prajna-pranab/SFT/STL/asm_SFT-Mk4-SFTRocker.stl

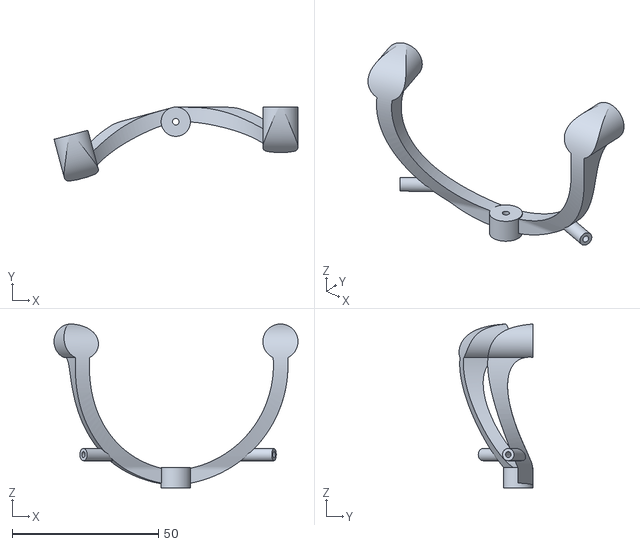
[picture p15: CAD file, 2024-05-06]
STL/asm_SFT-Mk4-SFTRocker.stl
83.3 x 25.2 x 56.0
