prajna-pranab/SFT/STL/asm_SFT-Mk4-SFTFlywheel Axle.stl

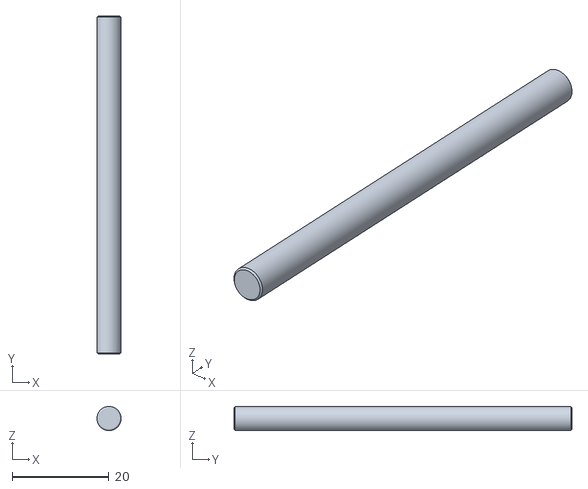
[picture p16: CAD file, 2024-05-06]
STL/asm_SFT-Mk4-SFTFlywheel Axle.stl
5.00 x 70.0 x 5.00
