prajna-pranab/SFT/STL/asm_SFT-Mk4-SFTSlider Block.stl

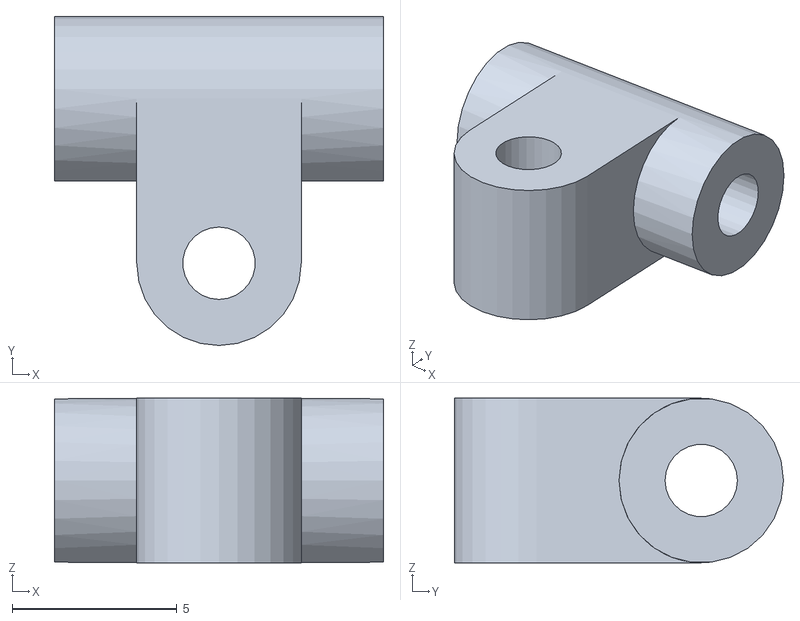
[picture p17: CAD file, 2024-05-06]
STL/asm_SFT-Mk4-SFTSlider Block.stl
10.0 x 10.0 x 5.00
