prajna-pranab/SFT/STL/asm_SFT-Mk4-SFTPin Bar.stl

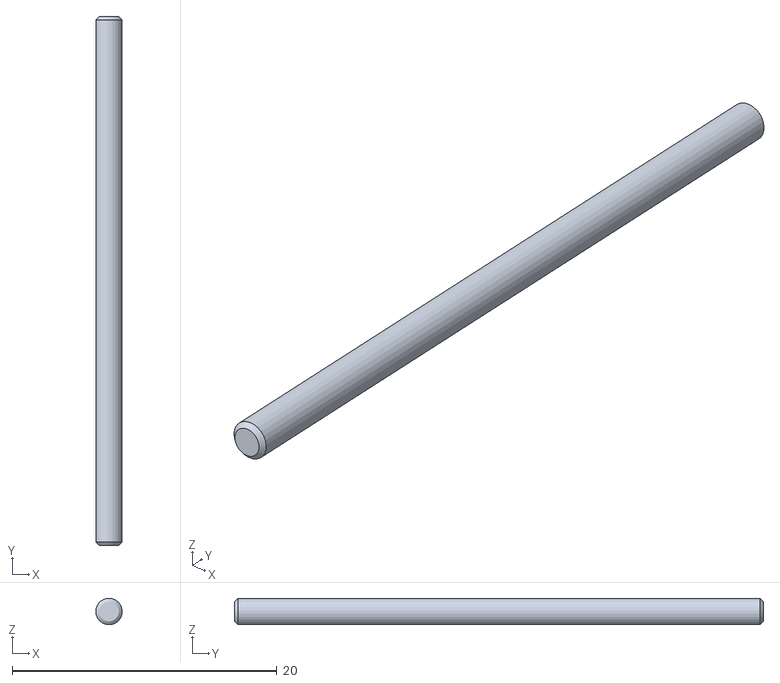
[picture p18: CAD file, 2024-05-06]
STL/asm_SFT-Mk4-SFTPin Bar.stl
2.00 x 40.0 x 2.00
