prajna-pranab/SFT/STL/asm_SFT-Mk4-SFTFlywheel Weight.stl

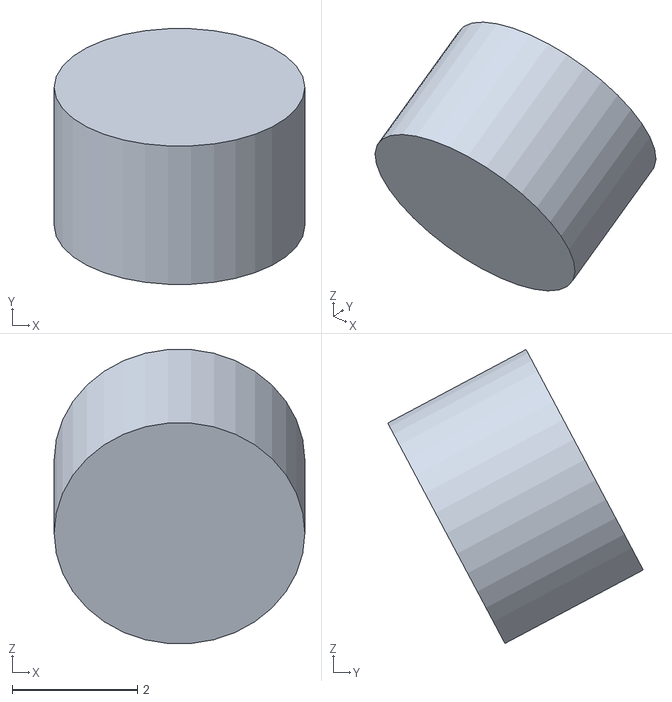
[picture p19: CAD file, 2024-05-06]
STL/asm_SFT-Mk4-SFTFlywheel Weight.stl
4.00 x 4.08 x 4.69
