prajna-pranab/SFT/asm_SFT-Mk4.FCStd

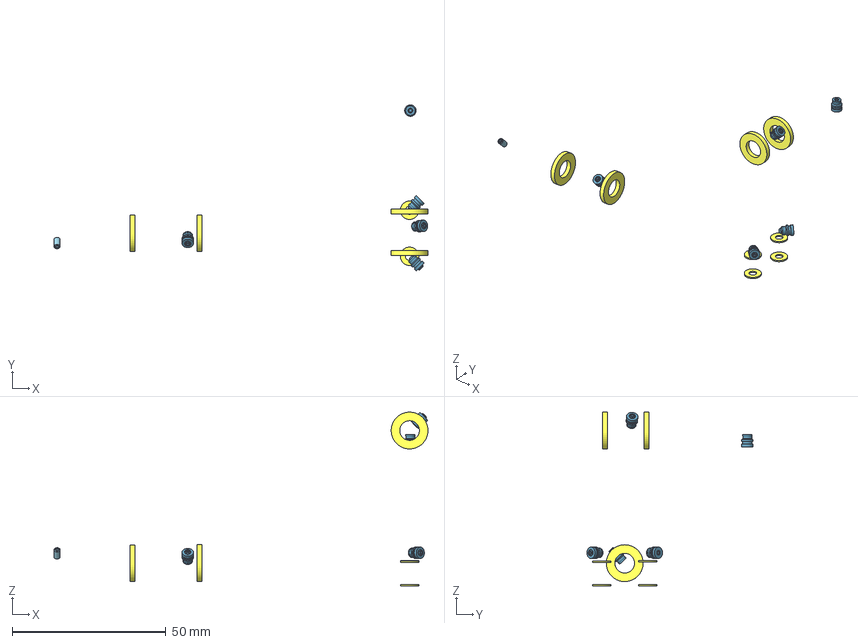
[picture p20: CAD file, 2024-04-28]
asm_SFT-Mk4.FCStd
121.8 x 54.1 x 56.6 mm
M6-Washer x 3
M2x4-Insert x 3
M2x4-Screw x 3
M6-Washer1773 x 3
M2x4-Insert19512 x 3
M2x5-Screw x 3
M2.5-Washer x 3
M2.5-Washer111 x 3
M2.5-Washer112 x 3
M2.5-Washer113 x 3
M2x4-Insert19513 x 3
M2x5-Screw001 x 3
M6-Washer1778 x 3
M6-Washer1779 x 3
M2x4-Insert19516 x 3
M2x4-Screw19638 x 3
M2x4-Screw19639 x 3
M2x4-Insert19515 x 2
M2x4-Screw19635 x 2
