prajna-pranab/SFT/Handle.FCStd

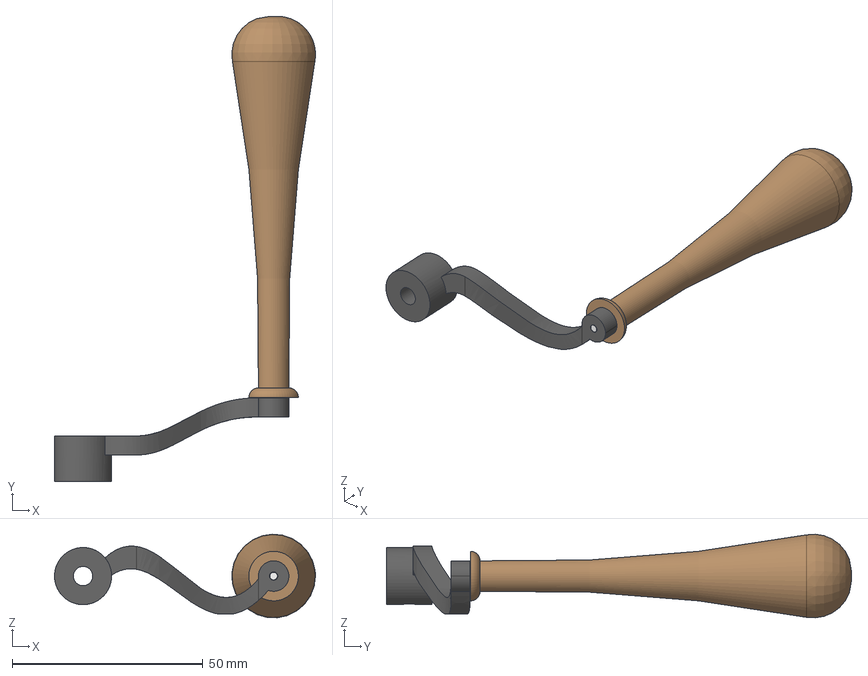
[picture p21: CAD file, 2024-06-03]
Handle.FCStd
68.5 x 122.1 x 21.9 mm
Nut Pocket
Rod
