prajna-pranab/SFT/Rotor Axle.FCStd

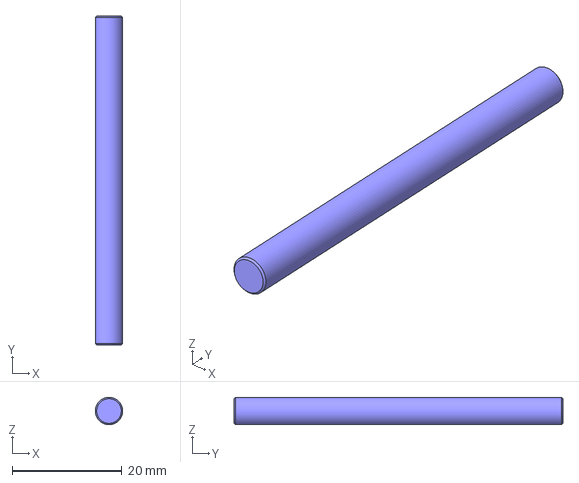
[picture p22: CAD file, 2024-06-03]
Rotor Axle.FCStd
5.00 x 60.0 x 5.00 mm
