prajna-pranab/SFT/Rotor.FCStd

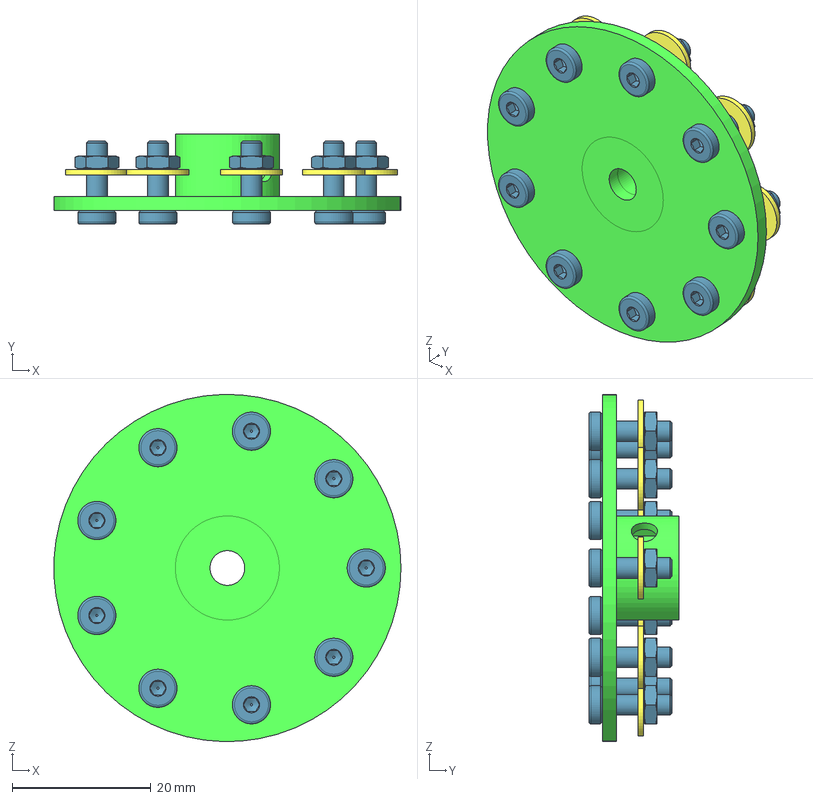
[picture p23: CAD file, 2024-06-03]
Rotor.FCStd
50.0 x 13.0 x 50.0 mm
M3x10-Screw089 x 2
M3x10-Screw090 x 2
M3x10-Screw091 x 2
M3x10-Screw092 x 2
M3x10-Screw x 2
M3x10-Screw093 x 2
M3x10-Screw094 x 2
M3x10-Screw095 x 2
M3x10-Screw096 x 2
M4-Washer x 2
M4-Washer097 x 2
M4-Washer098 x 2
M4-Washer099 x 2
M4-Washer100 x 2
M4-Washer101 x 2
M4-Washer102 x 2
M4-Washer103 x 2
M4-Washer104 x 2
M3-Nut x 2
M3-Nut105 x 2
M3-Nut106 x 2
M3-Nut107 x 2
M3-Nut108 x 2
M3-Nut109 x 2
M3-Nut110 x 2
M3-Nut111 x 2
M3-Nut112 x 2
Rotor Disk
