prajna-pranab/SFT/Pin Bar.FCStd

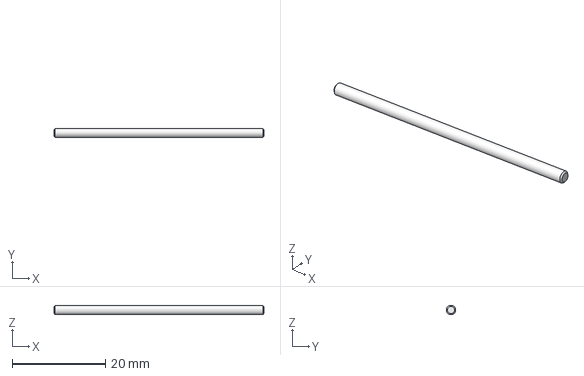
[picture p24: CAD file, 2024-06-02]
Pin Bar.FCStd
45.0 x 2.00 x 2.00 mm
