prajna-pranab/SFT/STL/Base-Base (Stands Unfused).stl

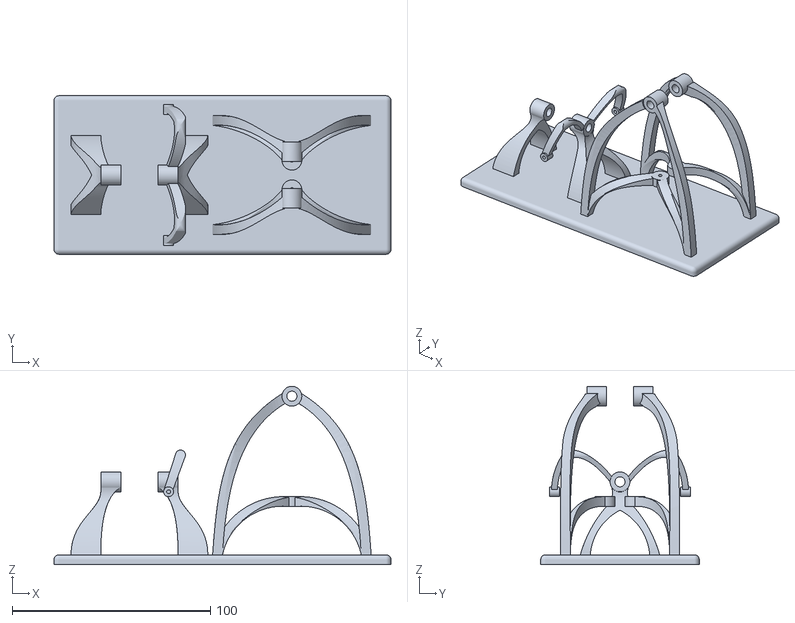
[picture p25: CAD file, 2024-05-26]
STL/Base-Base (Stands Unfused).stl
170.0 x 80.0 x 90.0
