prajna-pranab/SFT/Pin Block.FCStd

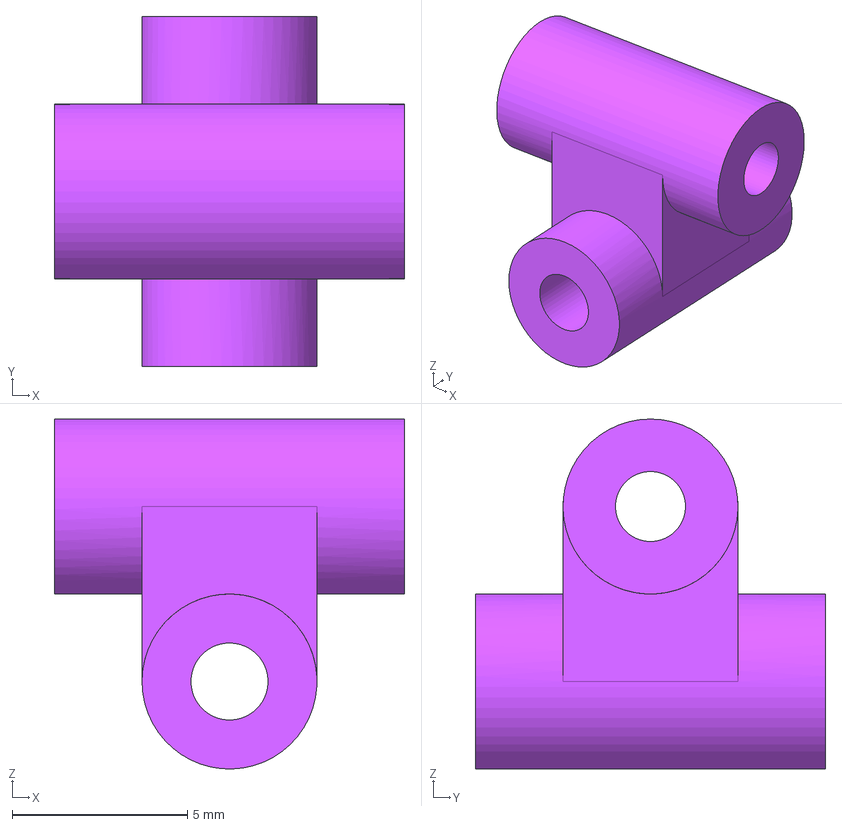
[picture p26: CAD file, 2024-06-02]
Pin Block.FCStd
10.0 x 10.0 x 10.00 mm
