prajna-pranab/SFT/Pully.FCStd

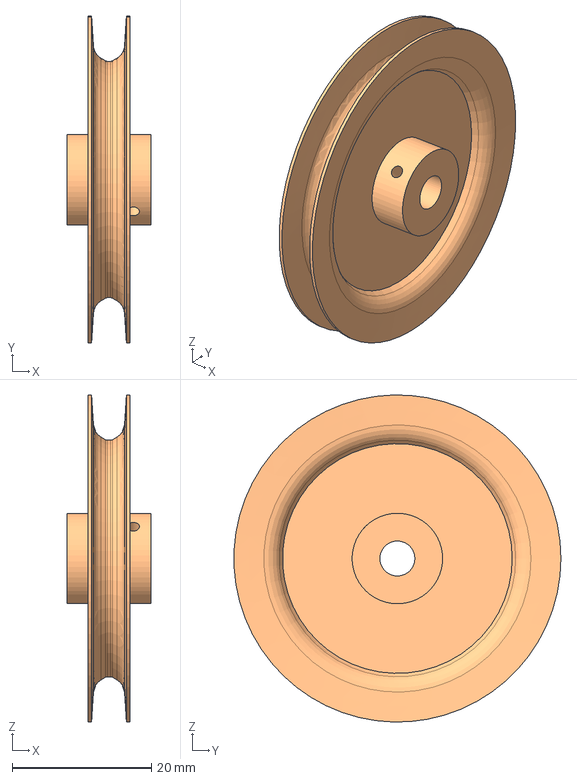
[picture p27: CAD file, 2024-05-27]
Pully.FCStd
12.0 x 47.0 x 47.0 mm
