prajna-pranab/SFT/Rocker Leg.FCStd

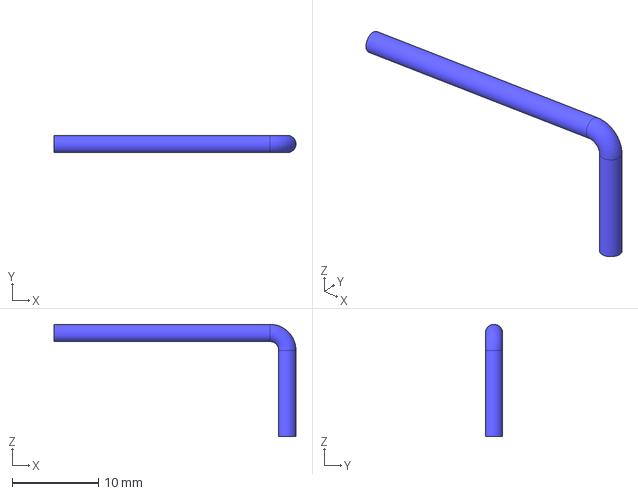
[picture p28: CAD file, 2024-05-27]
Rocker Leg.FCStd
28.0 x 2.00 x 13.0 mm
