prajna-pranab/SFT/Rocker.FCStd

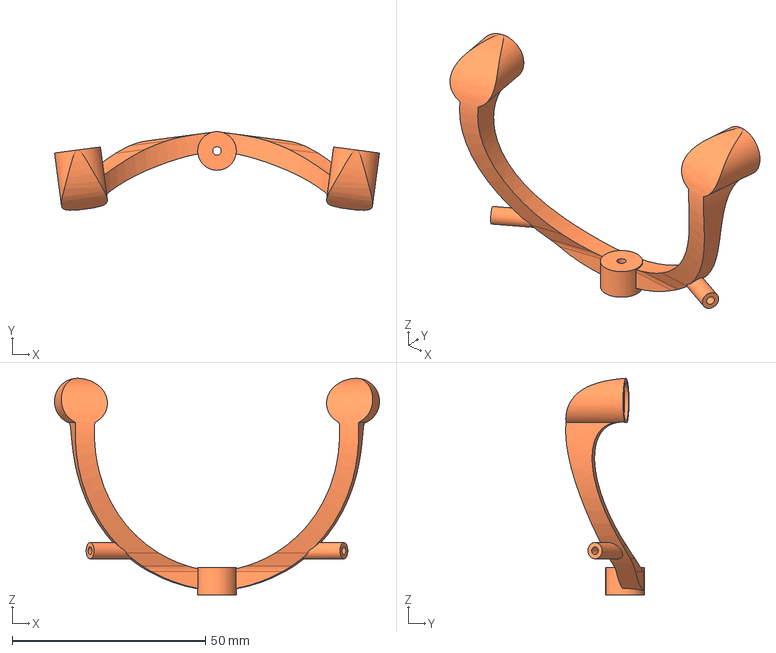
[picture p29: CAD file, 2024-05-27]
Rocker.FCStd
84.1 x 20.4 x 56.0 mm
