prajna-pranab/SFT/Slider Rod.FCStd

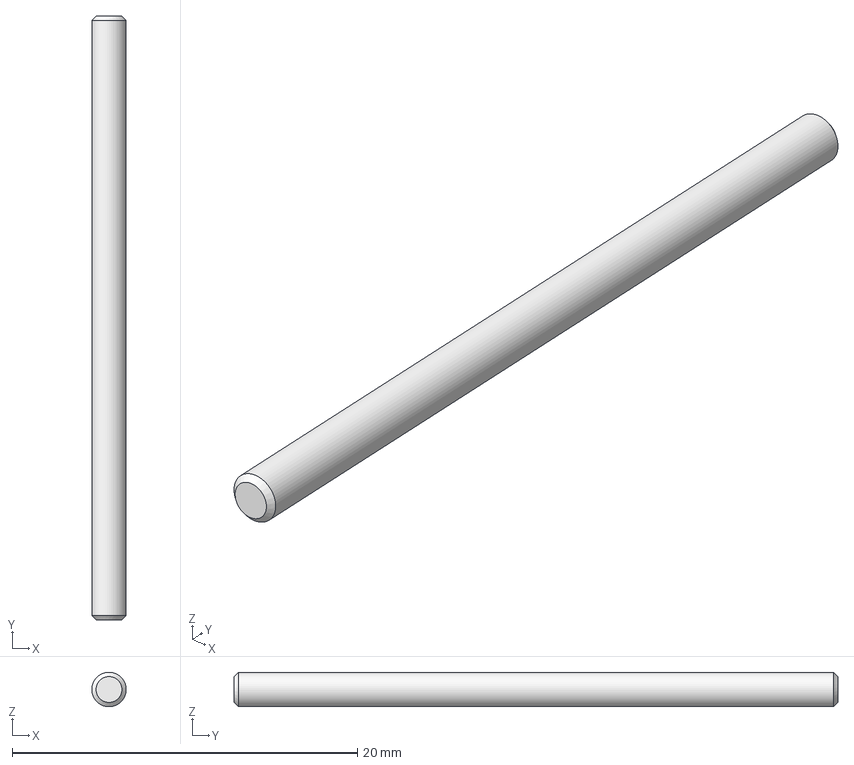
[picture p30: CAD file, 2024-04-28]
Slider Rod.FCStd
2.00 x 35.0 x 2.00 mm
