prajna-pranab/SFT/shaft.FCStd

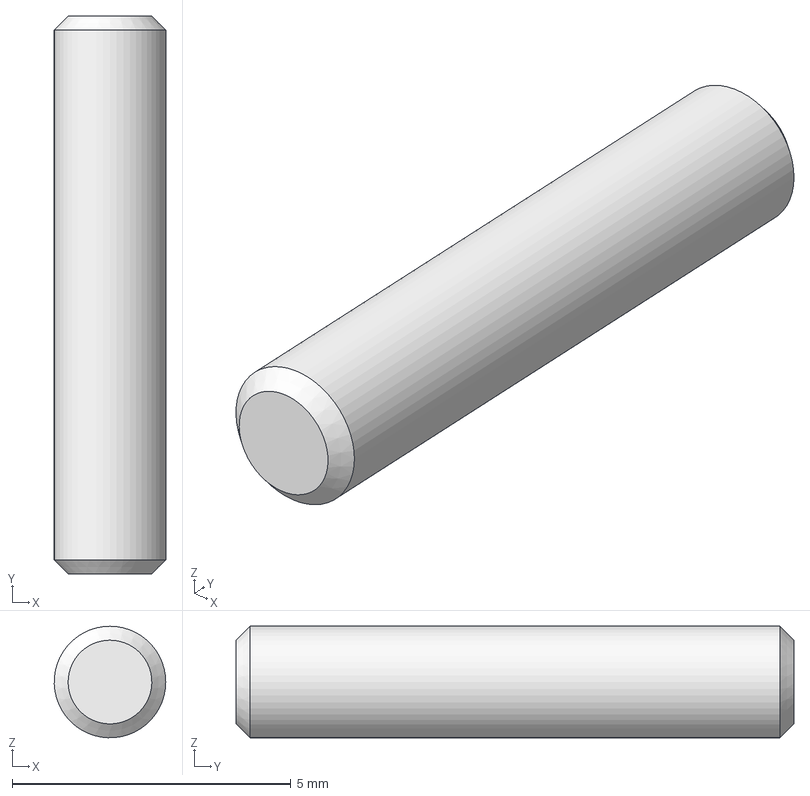
[picture p31: CAD file, 2024-04-28]
shaft.FCStd
2.00 x 10.0 x 2.00 mm
