prajna-pranab/SFT/Flywheel Weight.FCStd

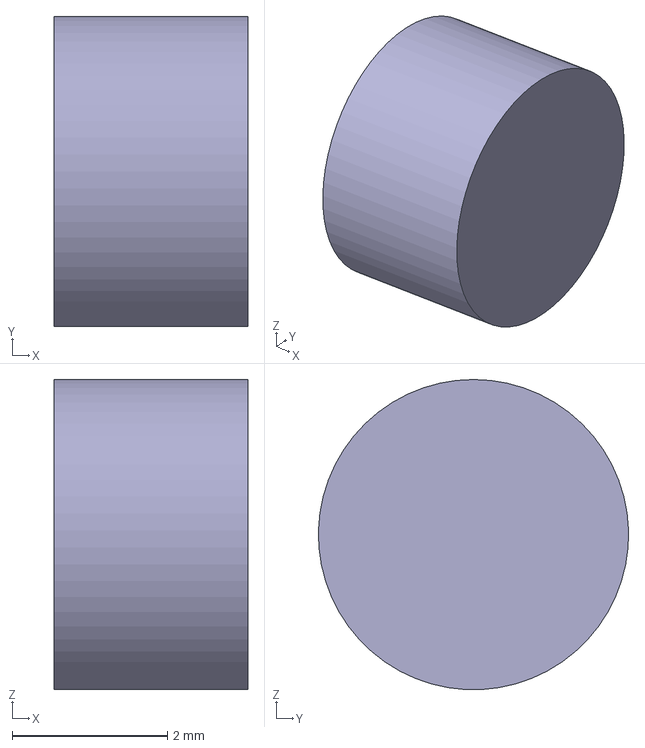
[picture p32: CAD file, 2024-04-28]
Flywheel Weight.FCStd
2.50 x 4.00 x 4.00 mm
