prajna-pranab/SFT/Magnet.FCStd

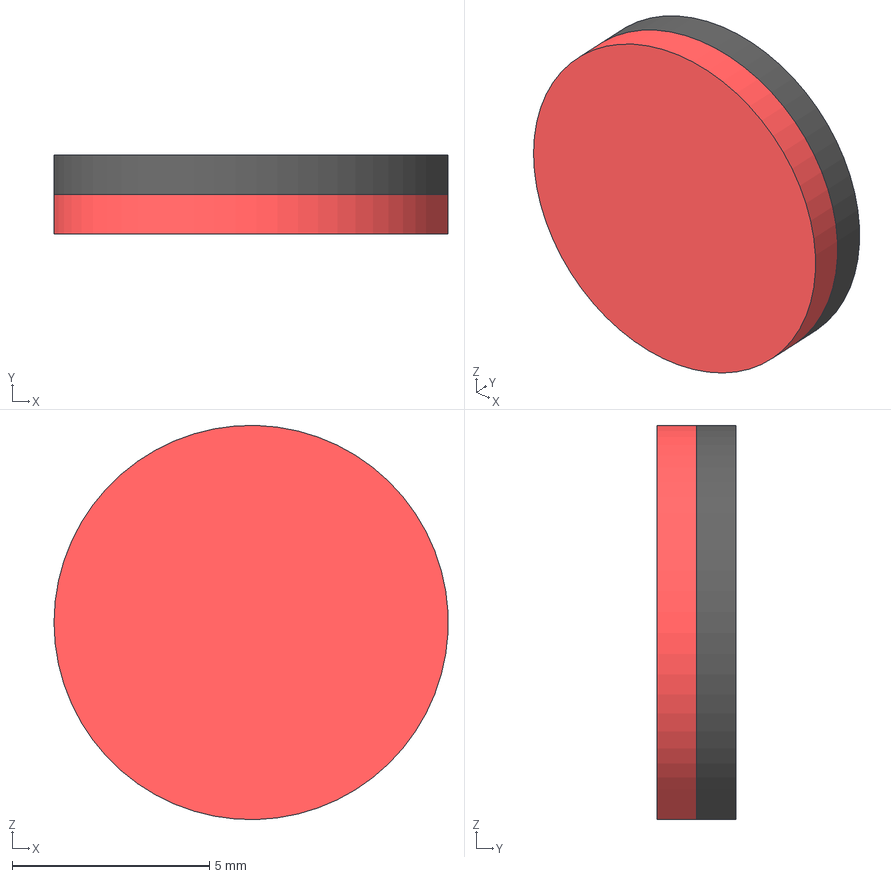
[picture p33: CAD file, 2024-04-28]
Magnet.FCStd
9.99 x 2.00 x 10.00 mm
SouthMagPole
NorthMagPole
